Prutsium/3D-Druckerplausch-Klipper/images/SupCRprobe.jpg

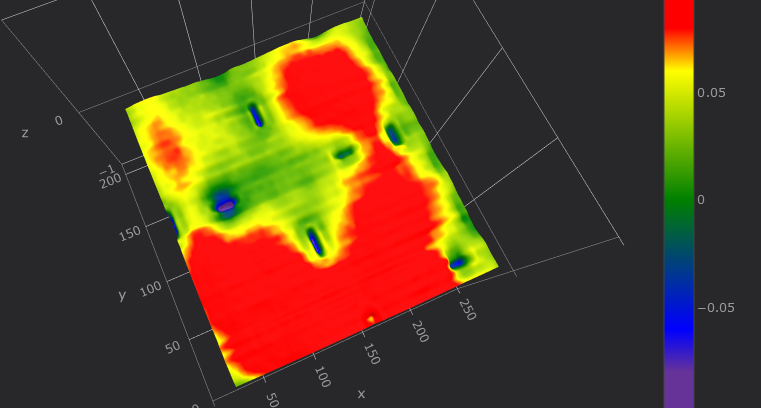
images/SupCRprobe.jpg
