Prutsium/3D-Druckerplausch-Klipper/doc/iobroker_blockly.png

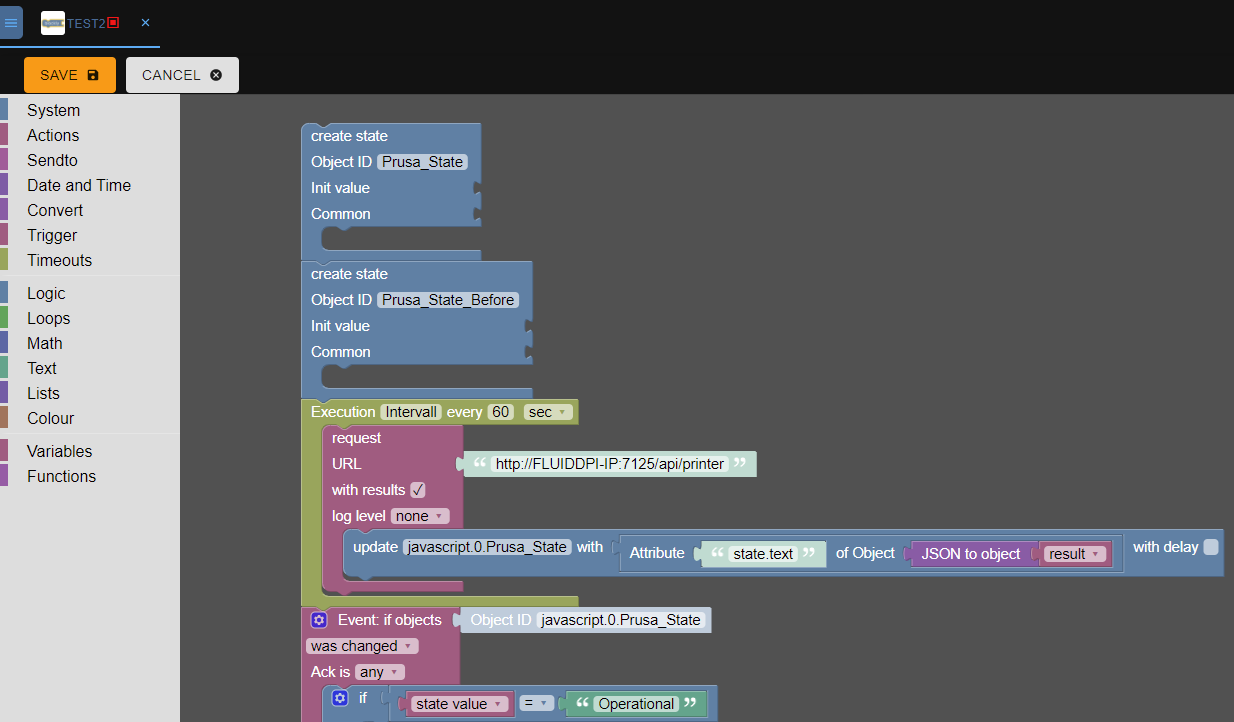
doc/iobroker_blockly.png
