Prutsium/3D-Druckerplausch-Klipper/images/slicer/SlicerFilamentCooling.jpg

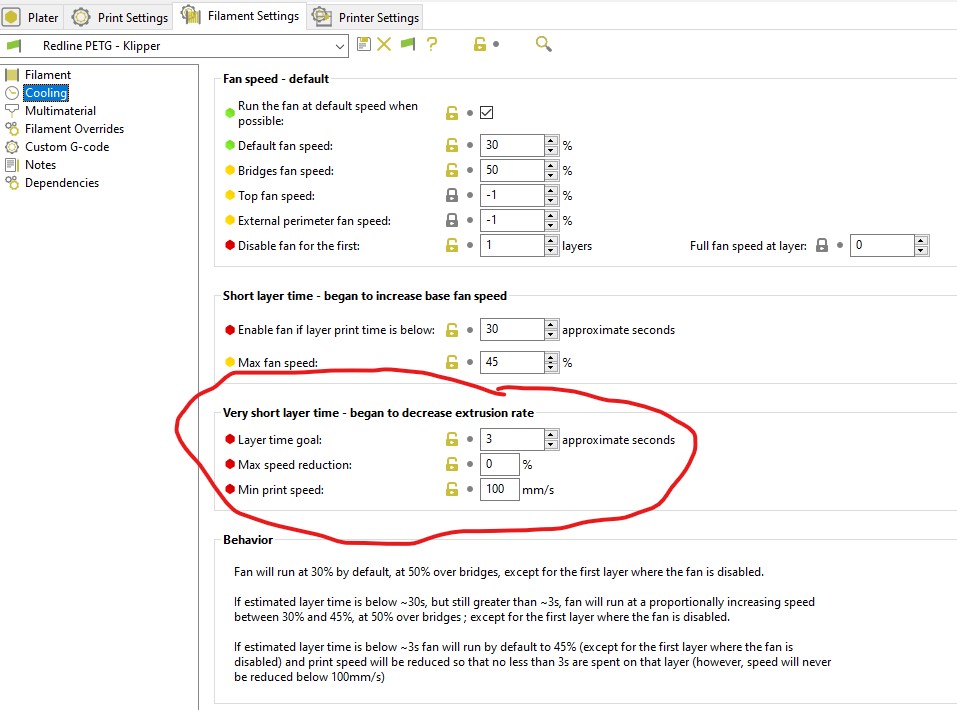
images/slicer/SlicerFilamentCooling.jpg
