Prutsium/3D-Druckerplausch-Klipper/images/slicer/SlicerFilamentCustomGcode.jpg

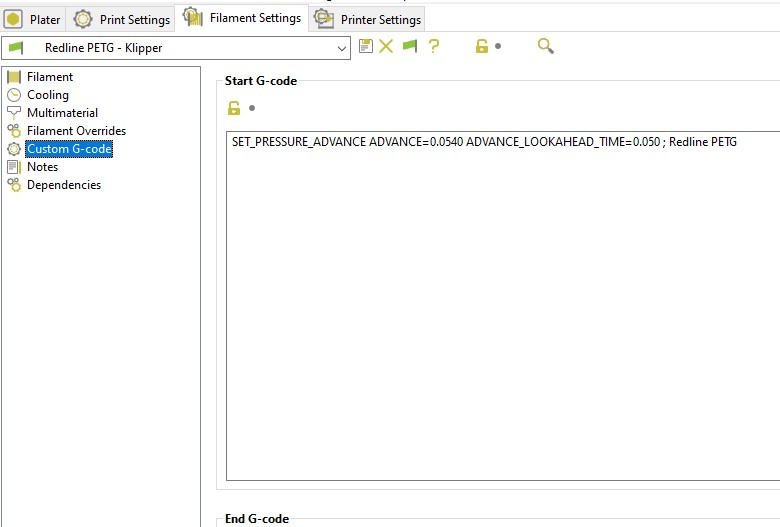
images/slicer/SlicerFilamentCustomGcode.jpg
