Prutsium/3D-Druckerplausch-Klipper/Klipper_cfg/Prusa_Universal_Config_Revised/Boards/Duet3Mini/JkXwMjGMcwQVRGnB.png

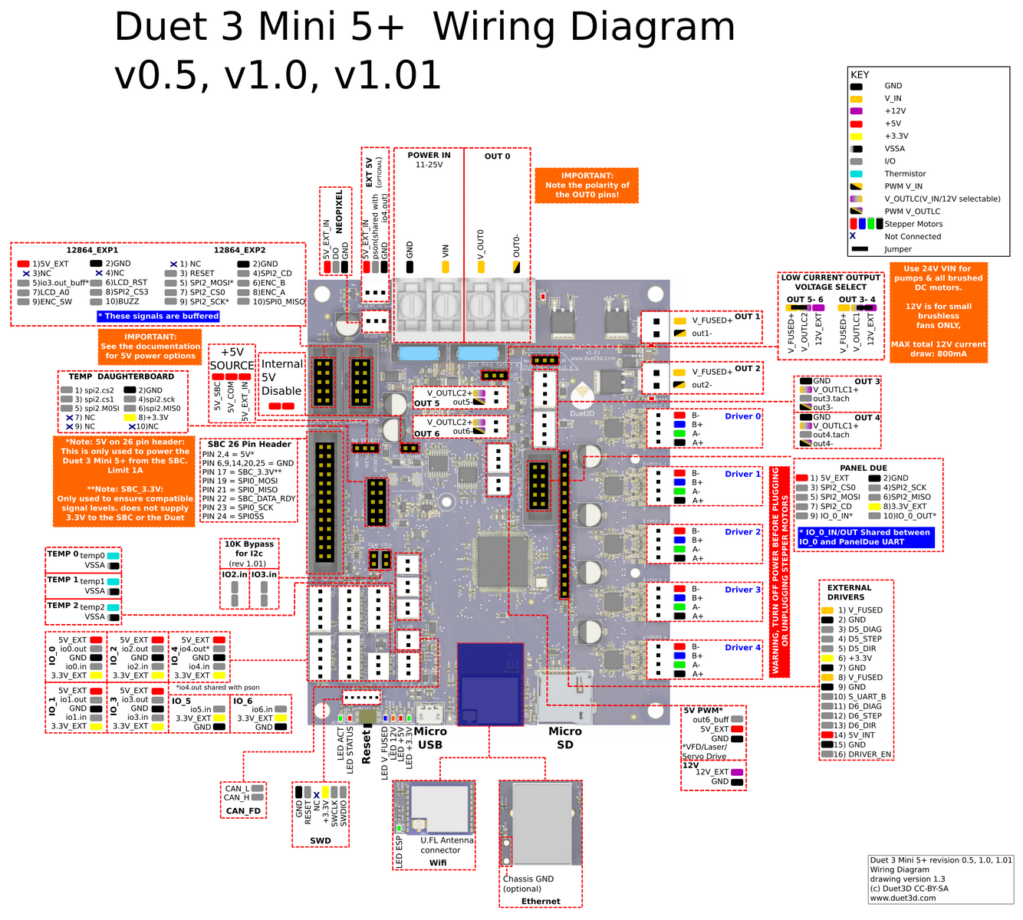
Klipper_cfg/Prusa_Universal_Config_Revised/Boards/Duet3Mini/JkXwMjGMcwQVRGnB.png
