Prutsium/3D-Druckerplausch-Klipper/images/slicer/SlicerPrinterCustomGcode.jpg

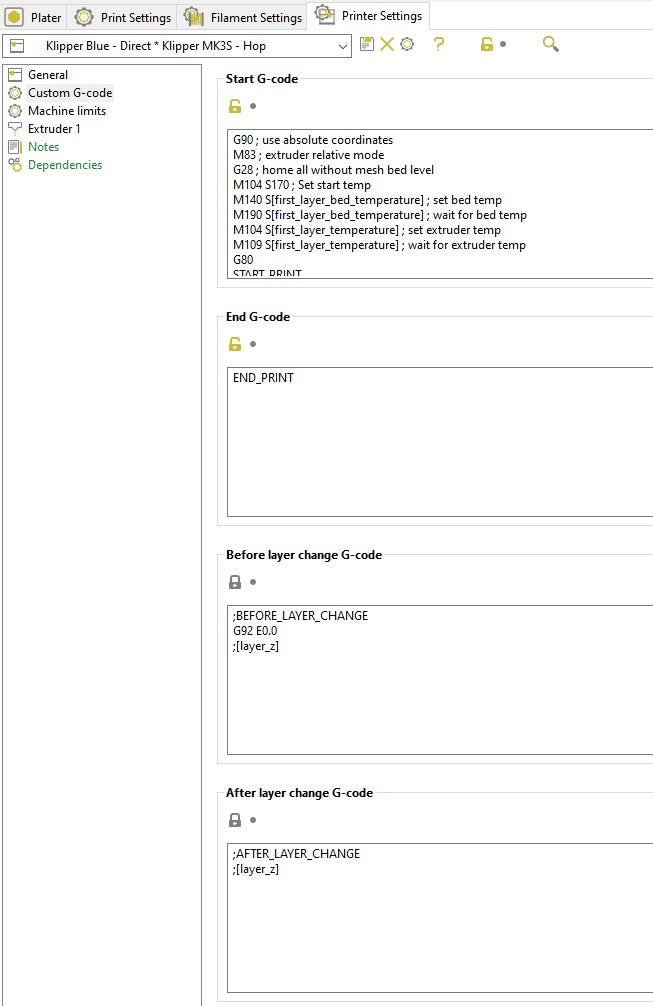
images/slicer/SlicerPrinterCustomGcode.jpg
