Prutsium/3D-Druckerplausch-Klipper/images/slicer/SlicerPrinterGeneral.jpg

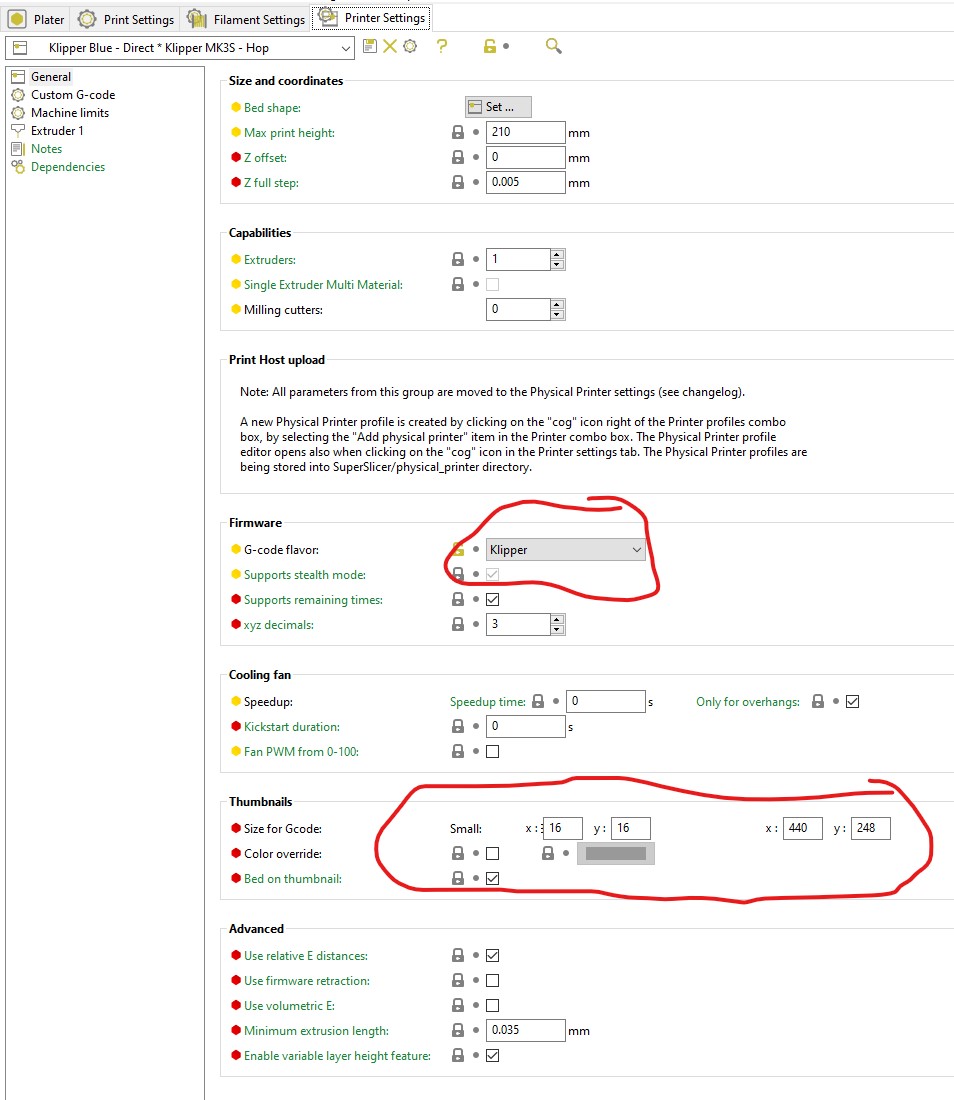
images/slicer/SlicerPrinterGeneral.jpg
