Prutsium/3D-Druckerplausch-Klipper/images/slicer/SlicerPrinterMachineLimits.jpg

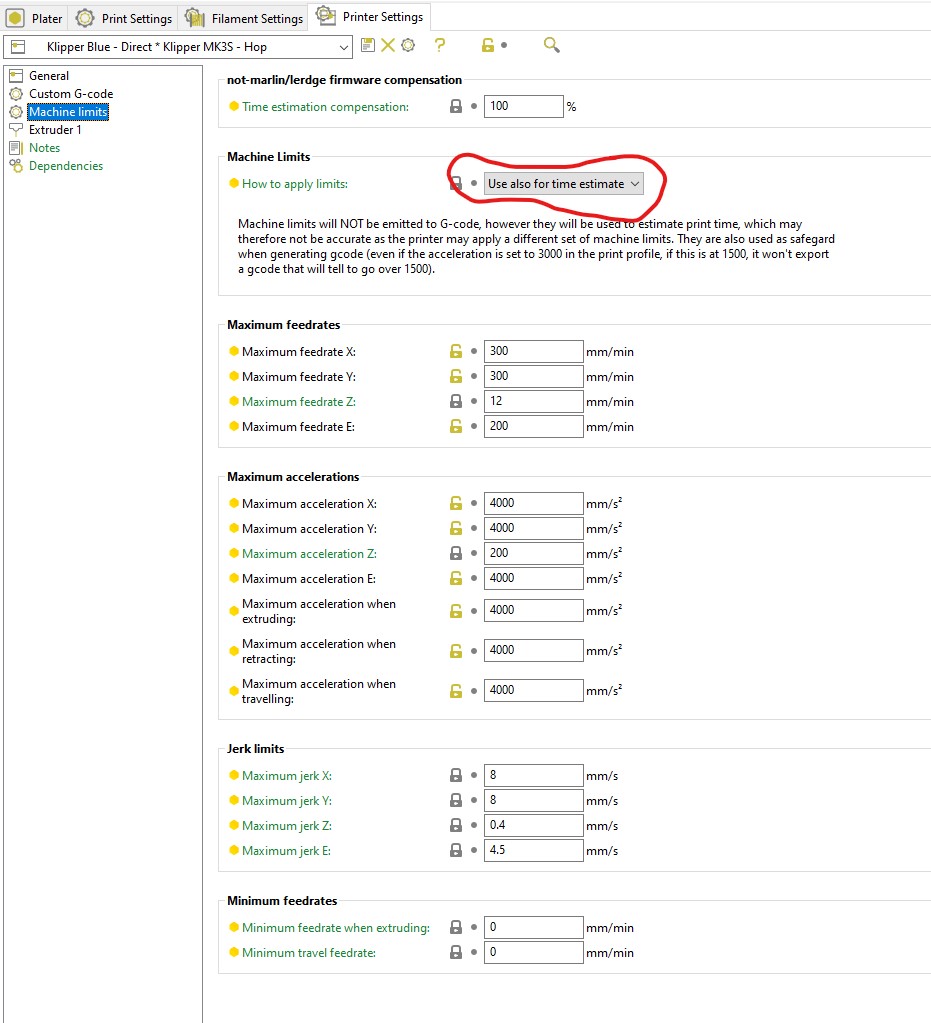
images/slicer/SlicerPrinterMachineLimits.jpg
