Prutsium/3D-Druckerplausch-Klipper/images/slicer/SlicerPrintSpeed.jpg

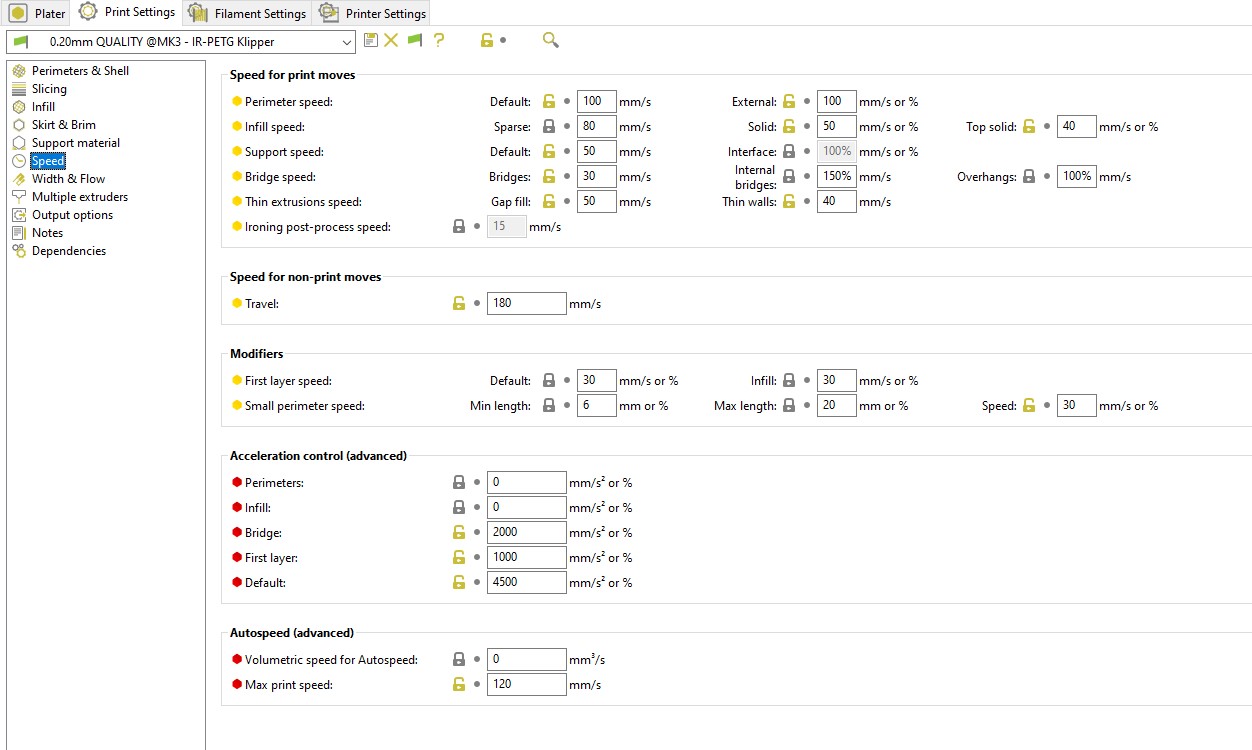
images/slicer/SlicerPrintSpeed.jpg
