Prutsium/3D-Druckerplausch-Klipper/Klipper_cfg/Prusa_MK3S_Duet_Klipper/shaper_calibrate_x.png

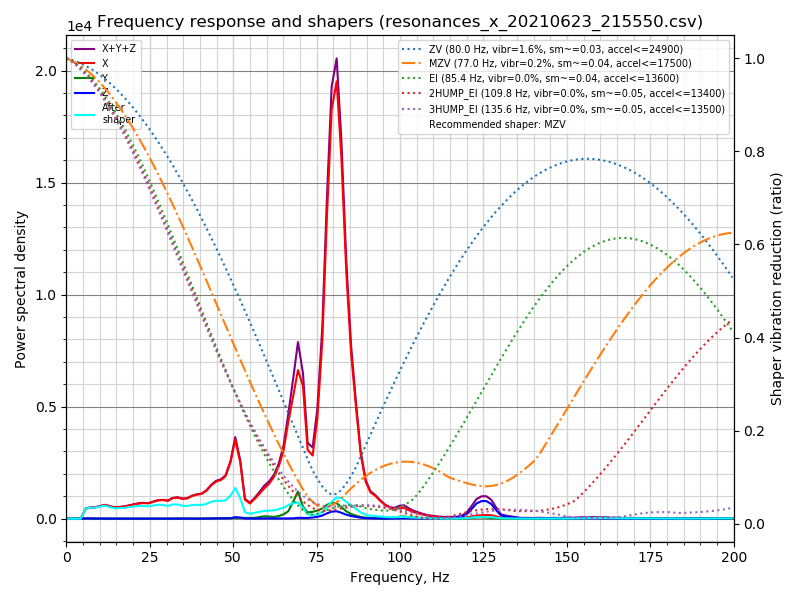
Klipper_cfg/Prusa_MK3S_Duet_Klipper/shaper_calibrate_x.png
