Prutsium/3D-Druckerplausch-Klipper/Klipper_cfg/Prusa_Einsy_MK3_cfg_Einsy/cfg/macros.cfg

#####################################################################
#   Einsy Macros
#####################################################################

[gcode_macro DUMP_PARAMETERS]
gcode:
  {% set parameters = namespace(output = '') %}
  {% for name1 in printer %}
    {% for name2 in printer[name1] %}
      {% set donotwant = ['bed_mesh'] %}
      {% if name1 is not in donotwant %}
        {% set param = "printer['%s'].%s = %s" % (name1, name2, printer[name1][name2]) %}
        {% set parameters.output = parameters.output +  param + "\n" %}
      {% endif %}
      {% else %}
        {% set param = "printer['%s'] = %s" % (name1, printer[name1]) %}
        {% set parameters.output = parameters.output +  param + "\n" %}
    {% endfor %}
  {% endfor %}
  {action_respond_info(parameters.output)}

[gcode_macro G80]
gcode:
 G28
 BED_MESH_CALIBRATE
 BED_MESH_PROFILE SAVE=Mesh
 G1 X0 Y0 Z0.4 F4000

[gcode_macro G81]
gcode:
 BED_MESH_OUTPUT
 
[respond]
default_type: command

[force_move]
enable_force_move: TRUE

[gcode_macro Tram_Z]
gcode:
    G28
    G1 X125 Y105 F2000
    G1 Z208 F1000
    FORCE_MOVE STEPPER=stepper_z Distance=10 Velocity=10
    G28 Z

[gcode_macro UP]
gcode:
    G1 Z100 F1500

[pause_resume]
# Keeps Debug LED off / not floating
[static_digital_output debug_led]
pins: !PB7

[output_pin BEEPER_pin]
pin: PH2
pwm: True
value: 0
shutdown_value:0
cycle_time: 0.001
scale: 1000

[gcode_macro M300]
default_parameter_S=1000
default_parameter_P=100
gcode:
 SET_PIN PIN=BEEPER_pin VALUE={S}
 G4 P{P}
 SET_PIN PIN=BEEPER_pin VALUE=0

[gcode_macro M600]
variable_extr_temp: 0
default_parameter_X: 100
default_parameter_Y: 0
default_parameter_Z: 10
gcode:
 PAUSE
 G91
 G1 E-.8 F2700
 G1 Z{Z}
 G90
 G1 X{X} Y{Y} F3000

[delayed_gcode clear_display]
initial_duration: 0.
gcode:
 M117

[menu __filament __load]
type: command
name: Load Filament
gcode:
    LOAD_FILAMENT

[menu __filament __unload]
type: command
name: Unload Filament
gcode:
    ORBITER_UNLOAD_FILAMENT

[menu __main __octoprint]
type: disabled
    
[virtual_sdcard]
path: ~/gcode_files

[gcode_macro CANCEL_PRINT]
rename_existing: BASE_CANCEL_PRINT
gcode:
    G91
    G1 X-2 Y-2 E-1 F300
    # Raise nozzle by 50mm
    G1 Z50 F3000
    G90
    TURN_OFF_HEATERS
    CLEAR_PAUSE
    SDCARD_RESET_FILE
    BASE_CANCEL_PRINT

[gcode_macro PAUSE]
rename_existing: BASE_PAUSE
default_parameter_X: 200    #edit to your park position
default_parameter_Y: 200    #edit to your park position
default_parameter_Z: 10     #edit to your park position
default_parameter_E: 1      #edit to your retract length
gcode:
    SAVE_GCODE_STATE NAME=PAUSE_state
    BASE_PAUSE
    G91
    G1 E-{E} F2100
    G1 Z{Z}
    G90
    G1 X{X} Y{Y} F6000

[gcode_macro RESUME]
rename_existing: BASE_RESUME
default_parameter_E: 1      # edit to your preferred retract length
gcode:
    G91
    G1 E{E} F2100
    G90
    RESTORE_GCODE_STATE NAME=PAUSE_state MOVE=1
    BASE_RESUME

[gcode_macro END_PRINT]
gcode:
    # Turn off bed, extruder, and fan
    M140 S0
    M104 S0
    M106 S0
    # Move nozzle away from print while retracting
    G91
    G1 X-2 Y-2 E-1 F300
    # Raise nozzle by 50mm
    G1 Z50 F3000
    G90
    # Disable steppers
    DISABLE_XY_STEPPERS
    #Disable Fan
    M107

[gcode_macro PURGE_LINE]
gcode:
    # Purge Line 
    G1 Y-3.0 F1000.0
    G1 Z0.4 F1000.0
    G1 X55.0 E10.0 F2000.0
    G1 Z0.3 F1000.0
    G92 E0.0
    G1 X240.0 E25.0  F2200.0
    G1 Y-2.0 F1000.0
    G1 X55.0 E25 F1400.0
    G1 Z0.20 F1000.0
    G1 X5.0 E4.0 F1000.0
    G92 E0.0 ; reset extruder distance position  
	
#####################################################################
#	START_PRINT Macro
#	To let this macro work optimal you have to add a few things to your slicer
#	Preferred is SuperSlicer as this can talk native Klipper Gcode
#	In the Start print Gcode of SuperSlicer make sure it contains only the following lines:
#	_DISPLAY_PLATE
#	SET_GCODE_VARIABLE MACRO=START_PRINT VARIABLE=BED_TEMP VALUE=[first_layer_bed_temperature]
#	SET_GCODE_VARIABLE MACRO=START_PRINT VARIABLE=EXTRUDER_TEMP VALUE=[first_layer_temperature]
#	M104 S0
#	M140 S0
#	START_PRINT
#
#	Also make sure you have tuned your Pressure Advance per Filament type / Setting and add the PA value to your Filament Settings Custom Gcode
#	For example:
#	SET_PRESSURE_ADVANCE ADVANCE=0.0625 ADVANCE_LOOKAHEAD_TIME=0.010
#####################################################################
[gcode_macro START_PRINT]
default_parameter_PA: 0.0520 #Default Pressure Advance when no setting is given in Slicer
default_parameter_BED_TEMP: 80
default_parameter_EXTRUDER_TEMP: 225
gcode:
    # metric values
    G21
    # use absolute coordinates
    G90
    # set extruder to relative mode
    M83
    # start with the fan off
    M107
    # home the printer
    {% if "xyz" not in printer.toolhead.homed_axes %}
    G28
    {% endif %}
    G0 Y0 X0 Z20 F3000
    # start bed heating
    M117 Bed to {BED_TEMP}
    M140 S{BED_TEMP}
    # set extruder temp to 170°C to avoid filament dripping
    {% if printer.extruder.temperature|int > 170 %}
        M117 Nozzle temp +170
    {% else %}
        M117 Preheating to 170
        M104 S170
    {% endif %}
    # move up to have room to clean nozzle if needed
    G0 Z100 F1000
    # set bed temp
    M140 S{BED_TEMP}
    # wait for bed temp
    M190 S{BED_TEMP}
    # home + mesh 
    {% if printer.bed_mesh.profile_name == "" %}
    G80
    {% endif %}
    G0 Y0 X0 Z20 F3000
    # clear pause
    CLEAR_PAUSE
    # zero the extruded length
    G92 E0.0
    # Move the nozzle near the bed
    # set and wait for nozzle/bed to reach temperature
    M117 Nozzle to {EXTRUDER_TEMP}
    M104 S{EXTRUDER_TEMP}       ; set extruder temp
    M109 S{EXTRUDER_TEMP}       ; wait for extruder temp
    # zero the extruded length
    G92 E0
    # purge line
    M117 Purge line
    UPDATE_DELAYED_GCODE ID=clear_display DURATION=4
	PURGE_LINE
    # start printing
    G1 F9000
    SET_PRESSURE_ADVANCE ADVANCE={PA} ADVANCE_LOOKAHEAD_TIME=0.010
    #M117 Printing with PA {PA}
    #UPDATE_DELAYED_GCODE ID=clear_display DURATION=4


##  Clear display after Duration 
[delayed_gcode _CLEAR_DISPLAY]
gcode:
  M117

[delayed_gcode clear_display]
initial_duration: 0.
gcode:
    M117

[gcode_macro Emergency_Lift_Z]
gcode:
    SET_KINEMATIC_POSITION X=0 Y=0 Z=0
    G91
    G1 Z+25 F1500
    G90
	
#####################################################################
#	Disable only XY Stepper Macro
#	As klipper disables all steppers with M84 this macro ensures only 
#	X & Y Stepper will be disabled to prevent sagging of the Z Steppers
#####################################################################
[gcode_macro DISABLE_XY_STEPPERS]
gcode:
	SET_STEPPER_ENABLE STEPPER=stepper_x ENABLE=0
	SET_STEPPER_ENABLE STEPPER=stepper_y ENABLE=0
