Prutsium/3D-Druckerplausch-Klipper/Klipper_cfg/Prusa_Universal_Config_Revised/Sensors/pi_adxl_mcu.cfg

#####################################################################
#   Second MCU on Pi
#####################################################################
[mcu rpi]
serial: /tmp/klipper_host_mcu

[adxl345]
cs_pin: rpi:None

[resonance_tester]
accel_chip: adxl345
probe_points:
    102,102,20  # an example
