Prutsium/3D-Druckerplausch-Klipper/Klipper_cfg/Prusa_Universal_Config_Revised/additions/git_backup.cfg

[gcode_shell_command backup_cfg]
command: /home/pi/klipper_config/additions/gitbackup.sh
timeout: 30.
verbose: True

[gcode_macro BACKUP_CFG]
gcode:
    RUN_SHELL_COMMAND CMD=backup_cfg
