Prutsium/3D-Druckerplausch-Klipper/Klipper_cfg/Prusa_Universal_Config_Revised/Sensors/z_probe_inversed.cfg

#####################################################################
#   Probe & Mesh
#####################################################################
[probe]
##  Inductive Probe
##  This probe is not used for Z height, only Z Tilt Adjustment
pin: !probe_pin
x_offset: 24
y_offset: 5
speed: 5.0
samples: 3
sample_retract_dist: 0.40
samples_tolerance: 0.2
lift_speed: 10
samples_result: average
