Prutsium/3D-Druckerplausch-Klipper/Klipper_cfg/Prusa_Universal_Config_Revised/Stepper/stepper_z1.cfg

#####################################################################
#   Z Stepper Settings for Dual Z Stepper driver printers only
#####################################################################
[stepper_z1]
step_pin: z1_step_pin
dir_pin: z1_dir_pin
enable_pin: !z1_enable_pin
