Prutsium/3D-Druckerplausch-Klipper/Klipper_cfg/Prusa with MMU_Octopus/cfg/tasmotaswitch.cfg

#Auto power off with a Tasmota PowerSwitch
[gcode_macro POWER_OFF_PRINTER]
gcode:
  {action_call_remote_method("set_device_power",
                             device="printer",
                             state="off")}
                             
[delayed_gcode delayed_printer_off]
initial_duration: 0.
gcode:
  {% if printer.idle_timeout.state == "Idle" %}
    POWER_OFF_PRINTER
  {% endif %}

[idle_timeout]
gcode:
  M117 Printer about to turn off
  TURN_OFF_MOTORS
  TURN_OFF_HEATERS
  UPDATE_DELAYED_GCODE ID=delayed_printer_off DURATION=30
